isol33t/viper/docs/images/split-expanded.png

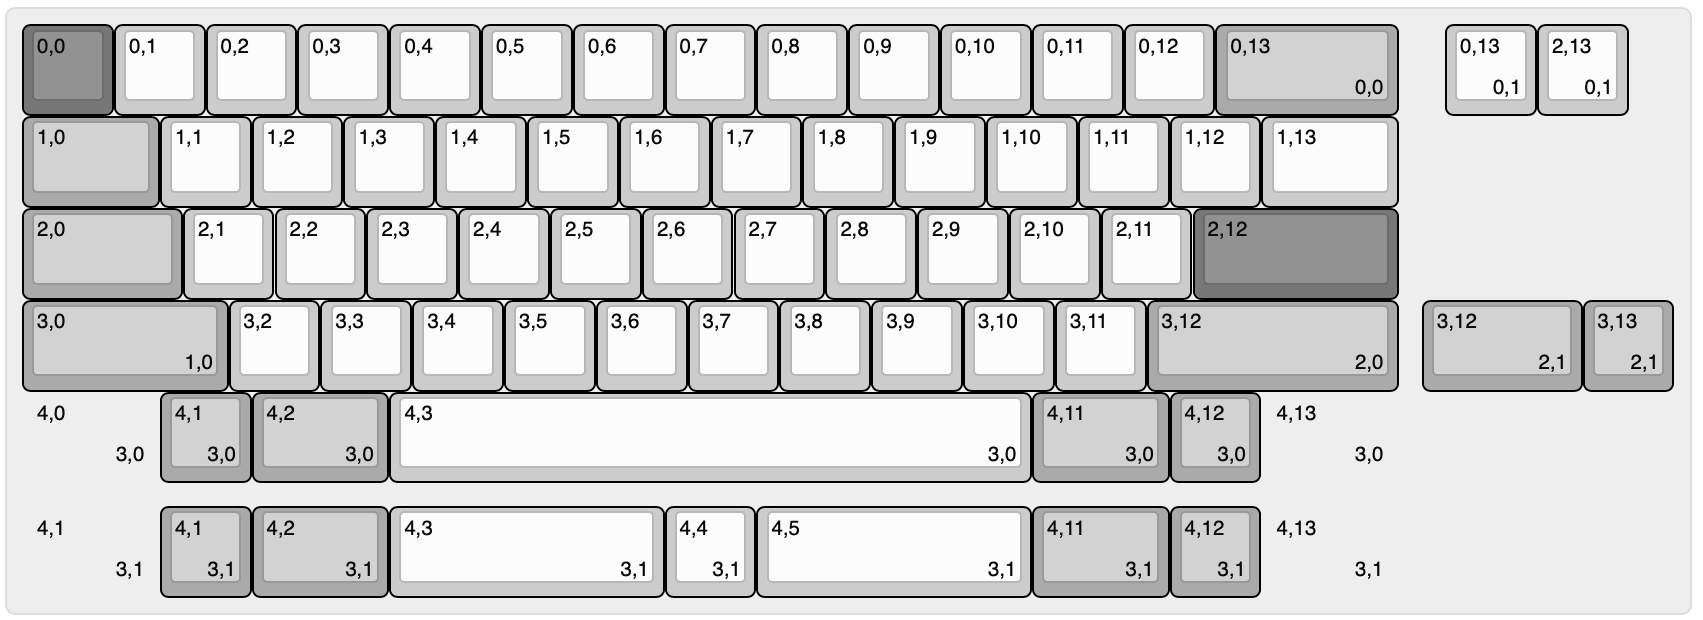
docs/images/split-expanded.png
